Reemuson/MENG4210-Assignment-2/HTML/images/cat_pdf_drill_map_Input-Protection-NPTH_drill_map.png

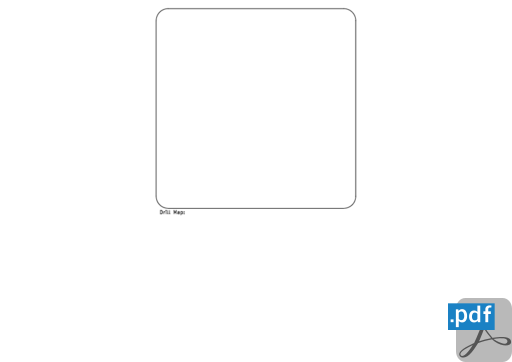
HTML/images/cat_pdf_drill_map_Input-Protection-NPTH_drill_map.png
