Reemuson/MENG4210-Assignment-2/HTML/images/cat_png_3d_viewer_top_Input-Protection-top.png

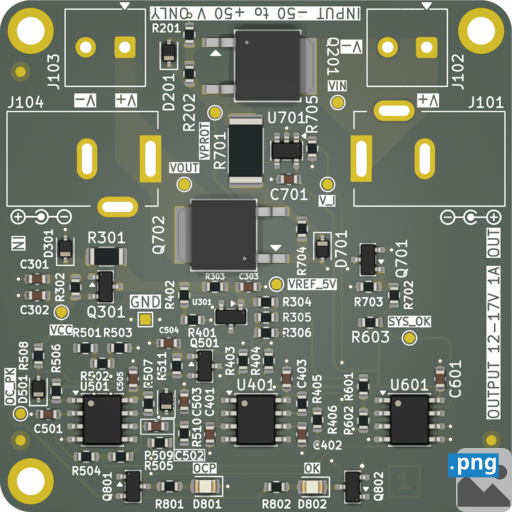
HTML/images/cat_png_3d_viewer_top_Input-Protection-top.png
